fabiobaltieri/power-manager/firmware/adc.c

/*
 * Copyright 2013 Fabio Baltieri (fabio.baltieri@gmail.com)
 *
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
 */

#include <avr/io.h>
#include <avr/interrupt.h>
#include <avr/sleep.h>
#include <util/delay.h>

#include "adc.h"

void adc_init(void)
{
	ADCSRA = ( (1 << ADEN)  | /* enable           */
		   (0 << ADSC)  | /* start conversion */
		   (0 << ADATE) | /* free running     */
		   (1 << ADIF)  | /* clear interrupts */
		   (0 << ADIE)  | /* interrupt enable */
		   (1 << ADPS2) | (1 << ADPS1) | (1 << ADPS0) );

	/* 12Mhz / 128 = 94kHz */

	/* turn on bandgap */
	ADMUX = _BV(REFS1) | _BV(REFS0);
}

void adc_stop(void)
{
	ADCSRA = 0x00; /* ADC disable */
}

void adc_set_channel(uint8_t channel)
{
	/* always use 1.1 Vref */
	ADMUX = _BV(REFS1) | _BV(REFS0) | (channel & 0xff);
}

uint16_t adc_get_value(void)
{
	ADCSRA |= _BV(ADSC);

	loop_until_bit_is_clear(ADCSRA, ADSC);

	return ADCW;
}
